ziyacaylan/Arduino-Kulucka-Makinesi/2.jpg

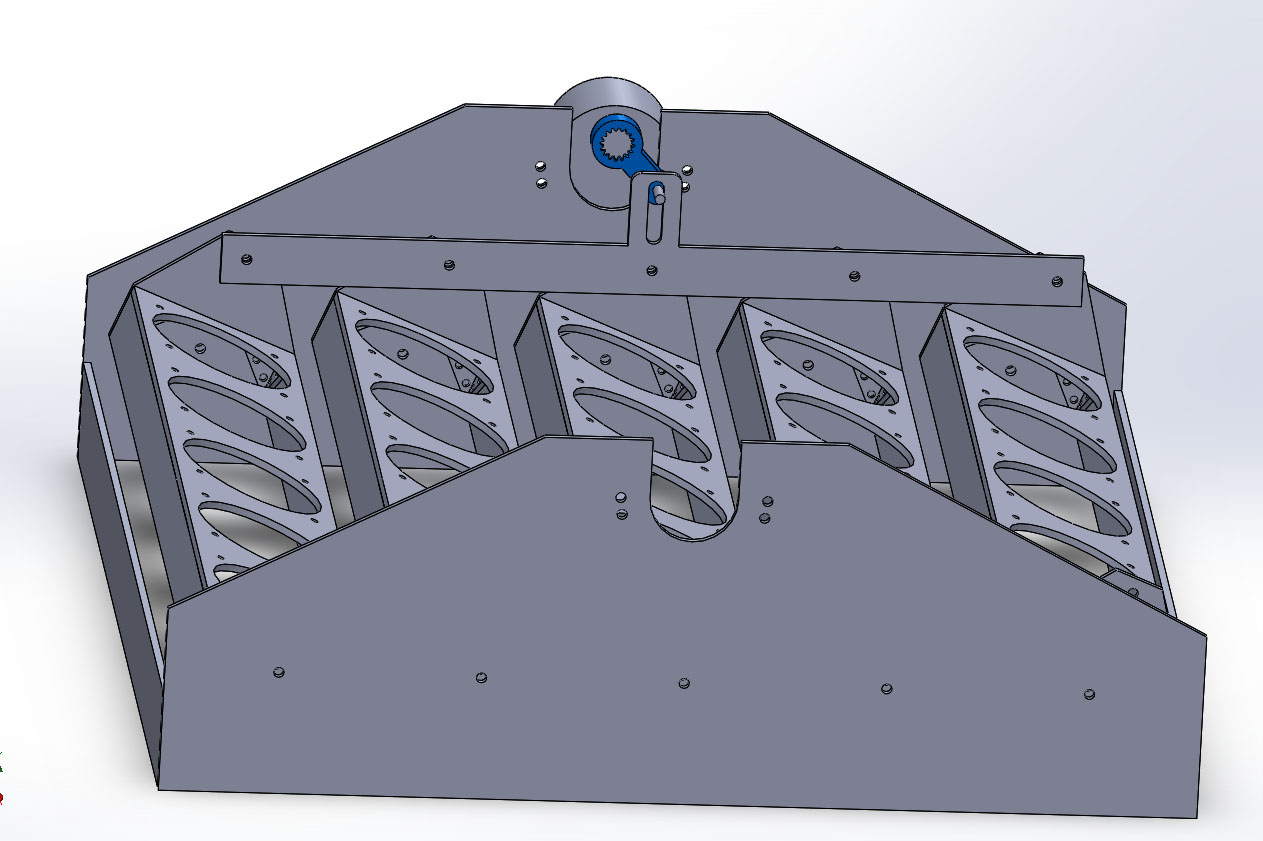
2.jpg
