ziyacaylan/Arduino-Kulucka-Makinesi/20190121_212128.jpg

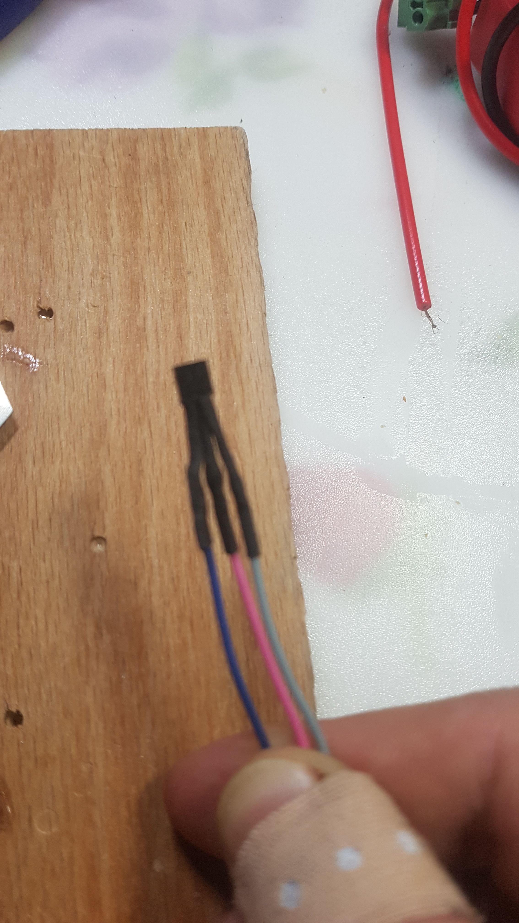
20190121_212128.jpg
