ziyacaylan/Arduino-Kulucka-Makinesi/20190127_220854.jpg

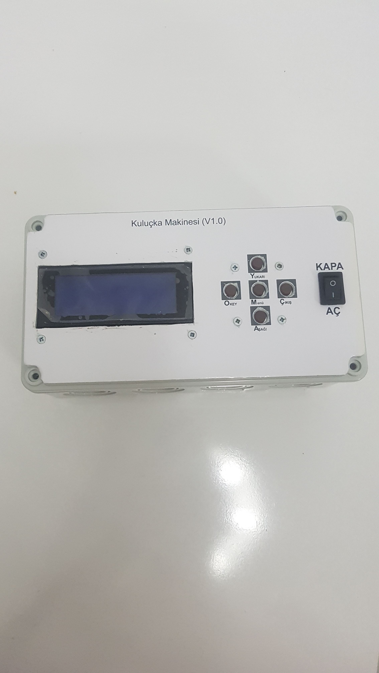
20190127_220854.jpg
