ziyacaylan/Arduino-Kulucka-Makinesi/20190207_001542.jpg

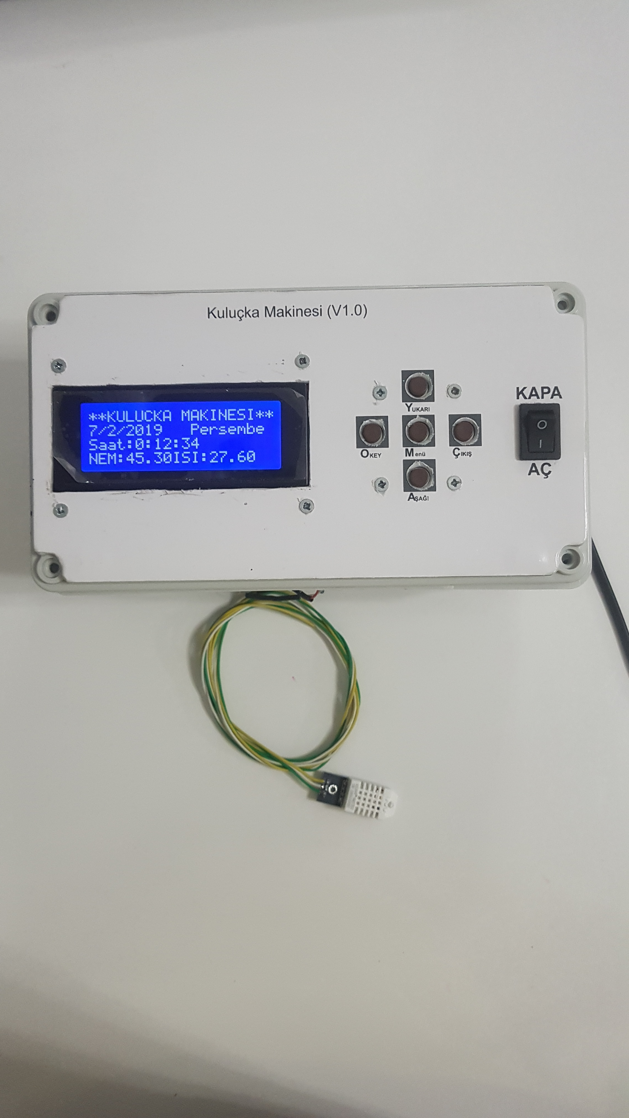
20190207_001542.jpg
