ziyacaylan/Arduino-Kulucka-Makinesi/20190218_220722.jpg

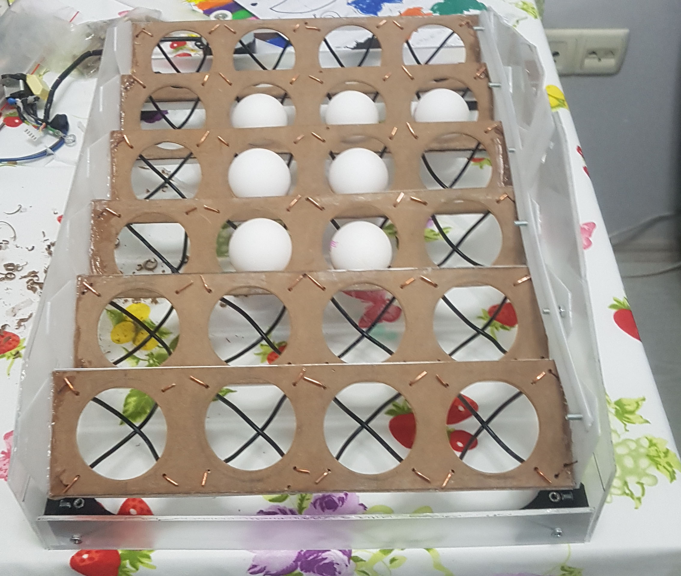
20190218_220722.jpg
