ziyacaylan/Arduino-Kulucka-Makinesi/20190220_000413.jpg

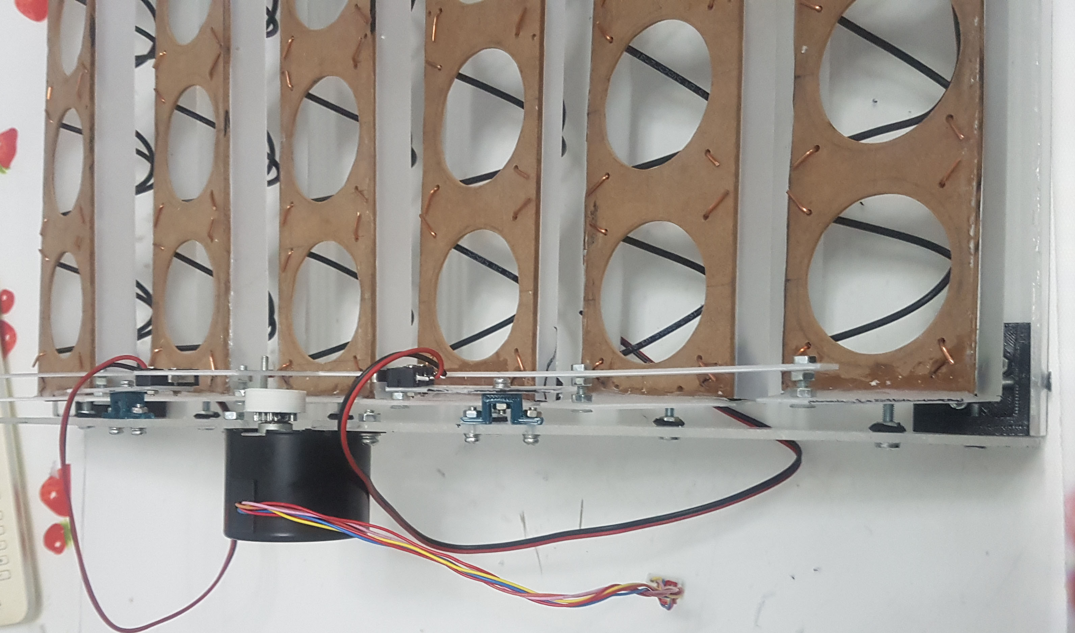
20190220_000413.jpg
