ziyacaylan/Arduino-Kulucka-Makinesi/20190220_000423.jpg

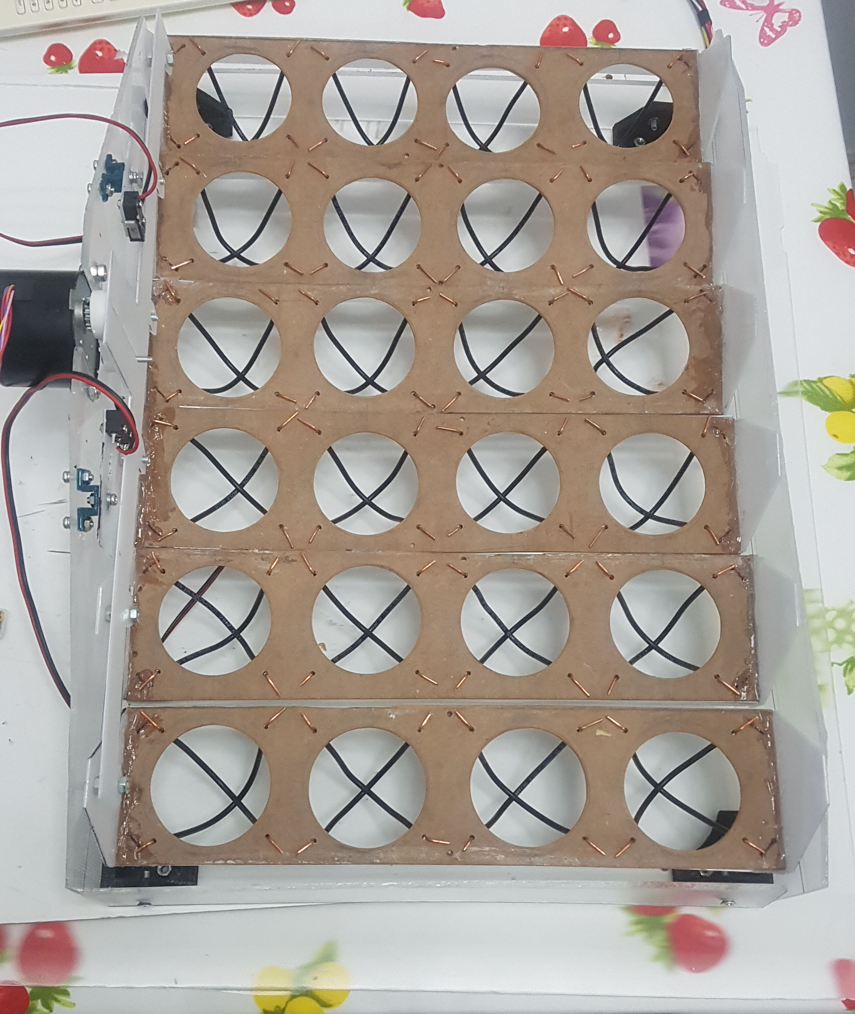
20190220_000423.jpg
