ziyacaylan/Arduino-Kulucka-Makinesi/20190220_000430.jpg

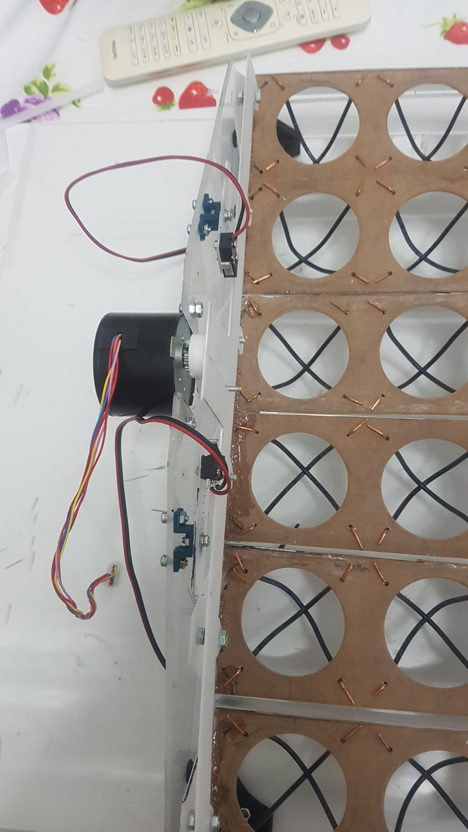
20190220_000430.jpg
