ziyacaylan/Arduino-Kulucka-Makinesi/20190223_140136.jpg

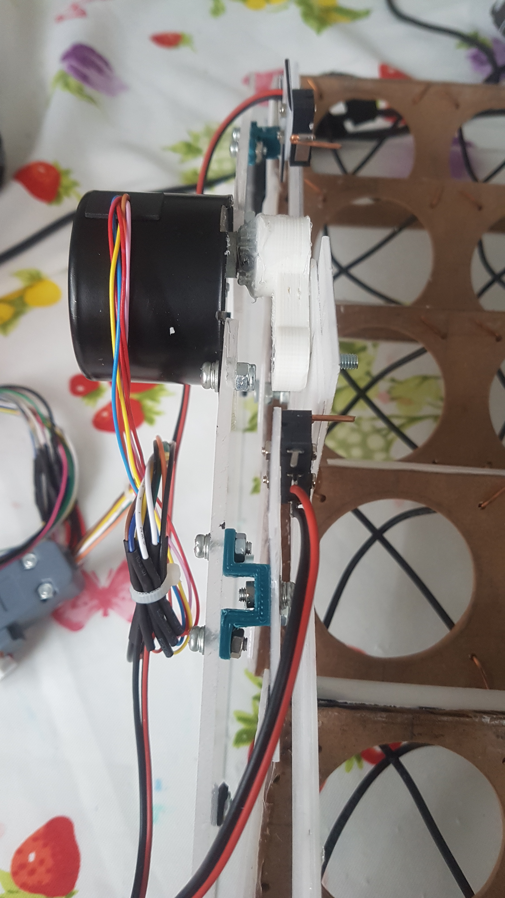
20190223_140136.jpg
