ziyacaylan/Arduino-Kulucka-Makinesi/20190223_140142.jpg

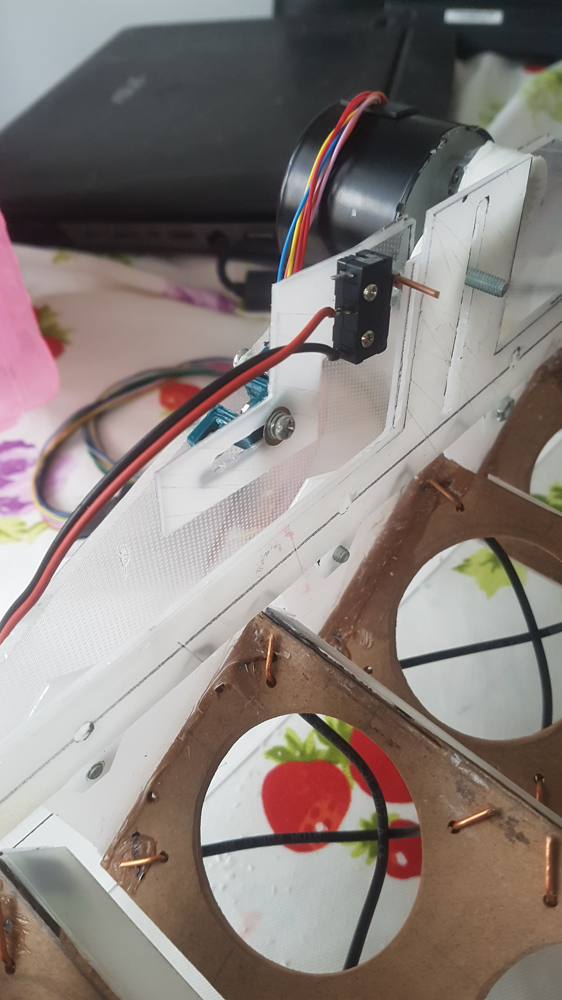
20190223_140142.jpg
