ziyacaylan/Arduino-Kulucka-Makinesi/20190223_140147.jpg

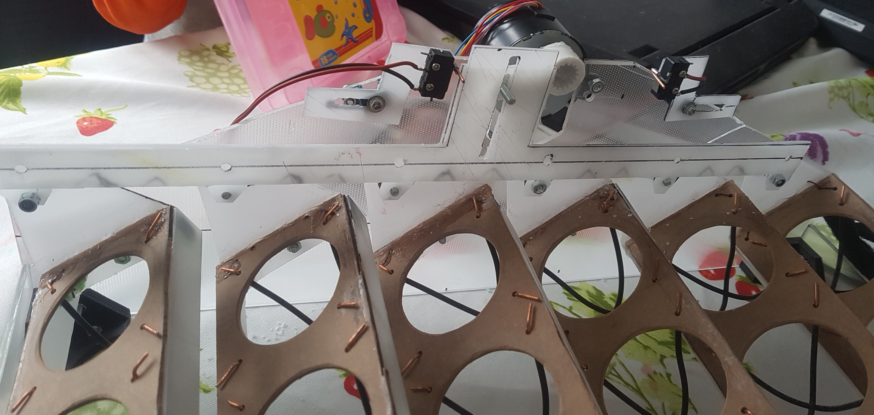
20190223_140147.jpg
