ziyacaylan/Arduino-Kulucka-Makinesi/20190223_140152.jpg

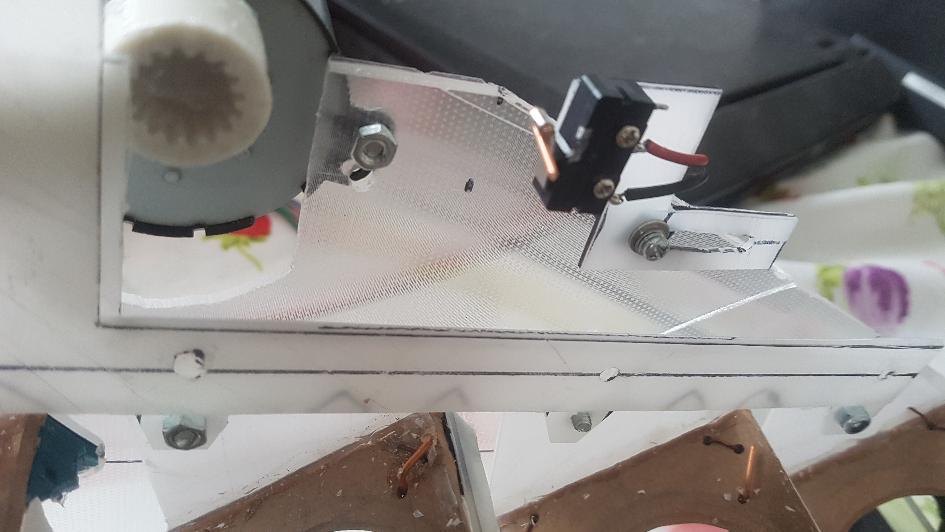
20190223_140152.jpg
