ziyacaylan/Arduino-Kulucka-Makinesi/20190223_140200.jpg

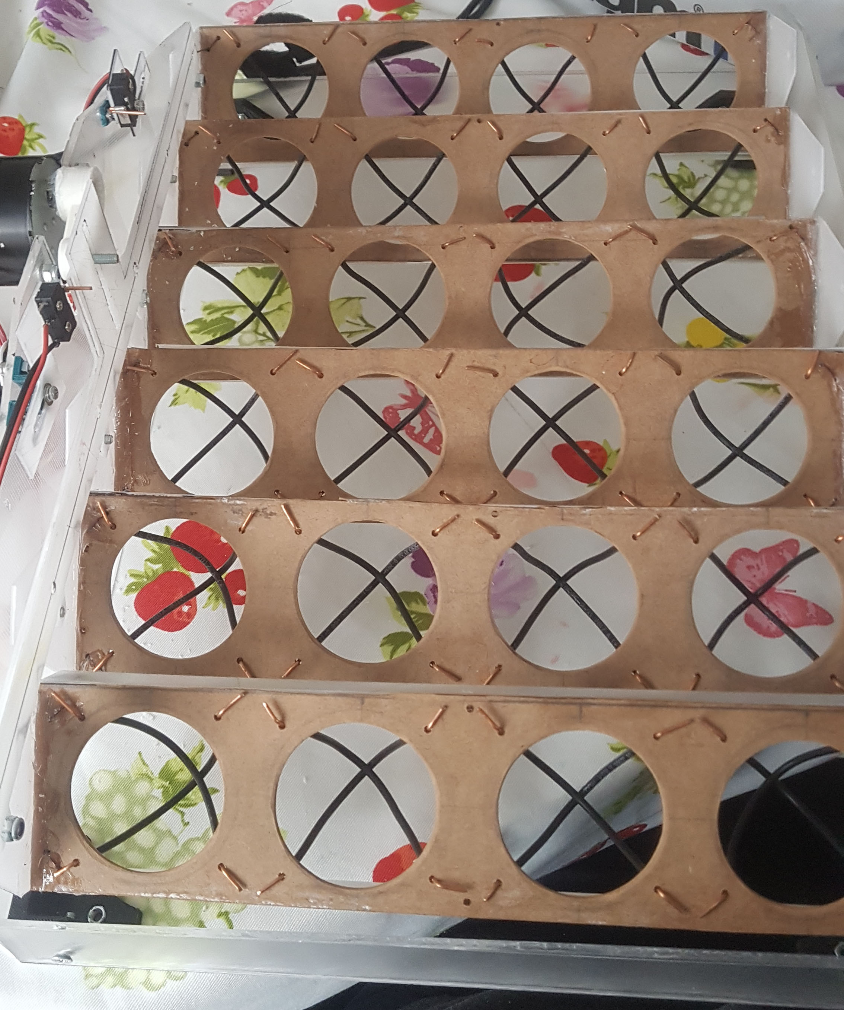
20190223_140200.jpg
