ziyacaylan/Arduino-Kulucka-Makinesi/20190223_235003.jpg

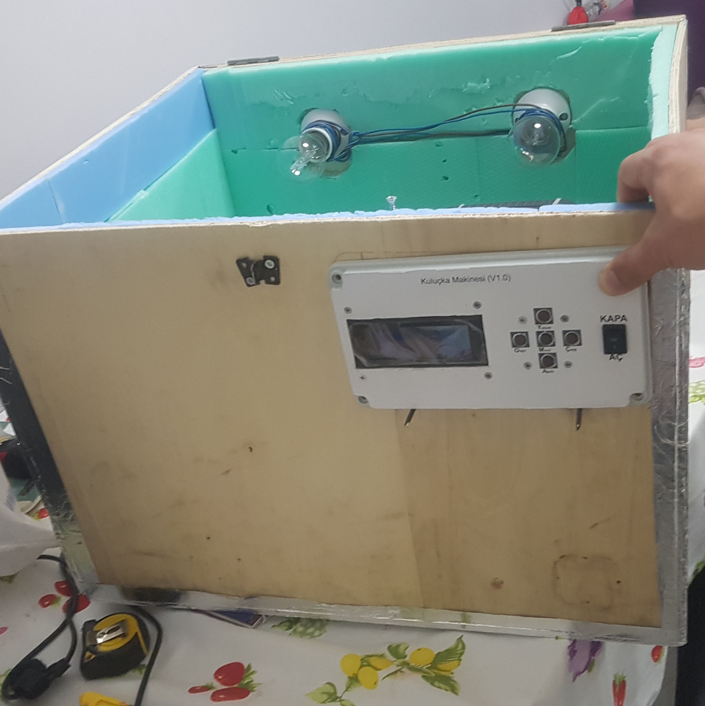
20190223_235003.jpg
