ziyacaylan/Arduino-Kulucka-Makinesi/20190223_235006.jpg

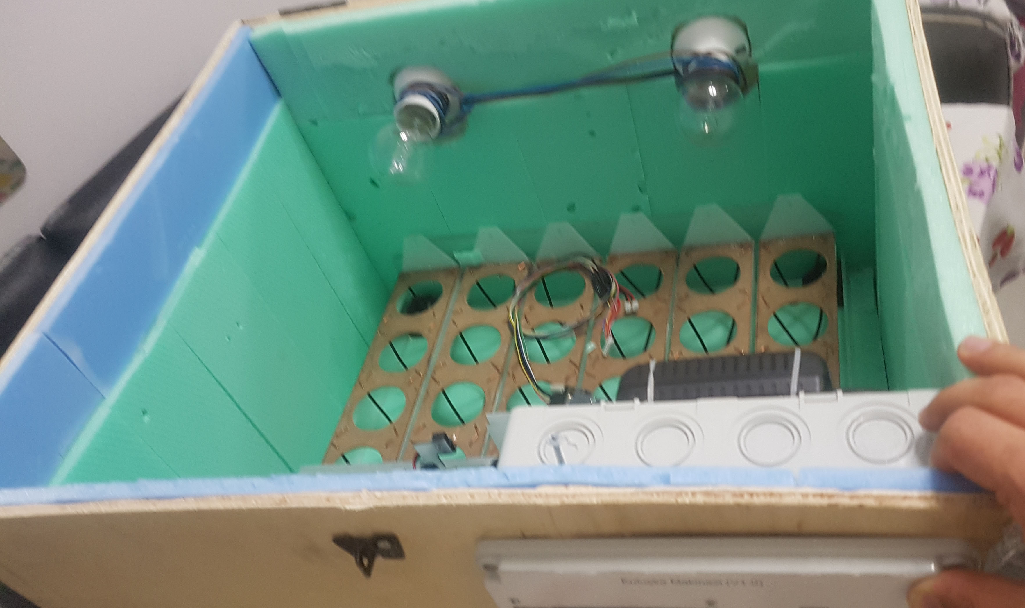
20190223_235006.jpg
