ziyacaylan/Arduino-Kulucka-Makinesi/20190223_235153.jpg

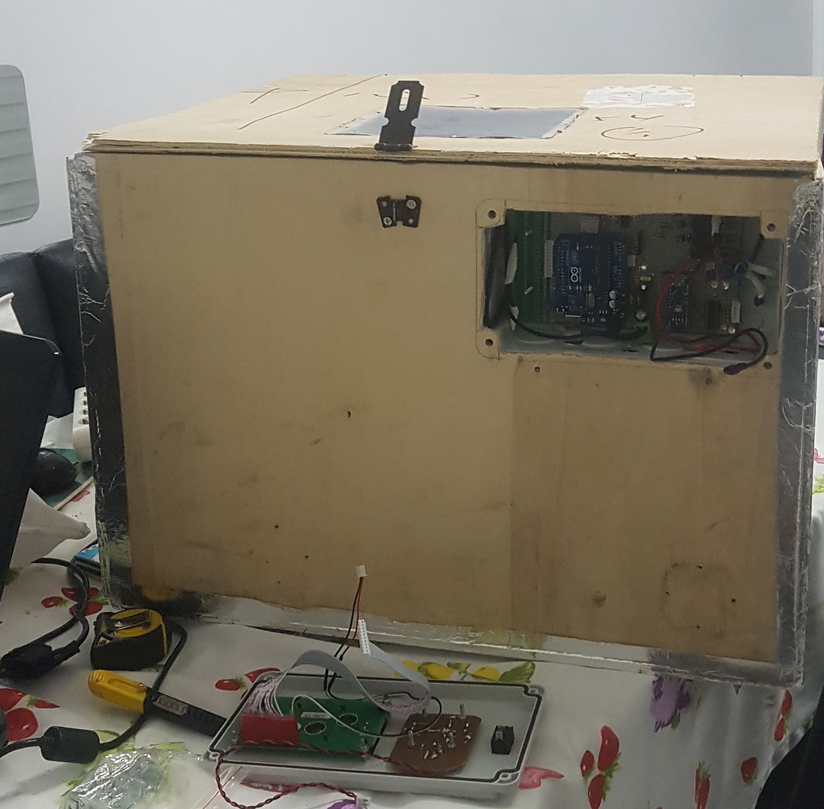
20190223_235153.jpg
