ziyacaylan/Arduino-Kulucka-Makinesi/20190223_235156.jpg

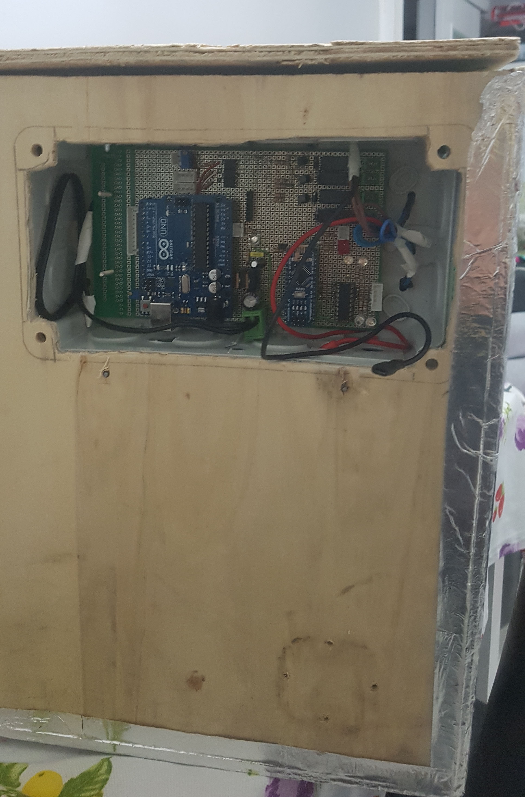
20190223_235156.jpg
