ziyacaylan/Arduino-Kulucka-Makinesi/20190310_233816.jpg

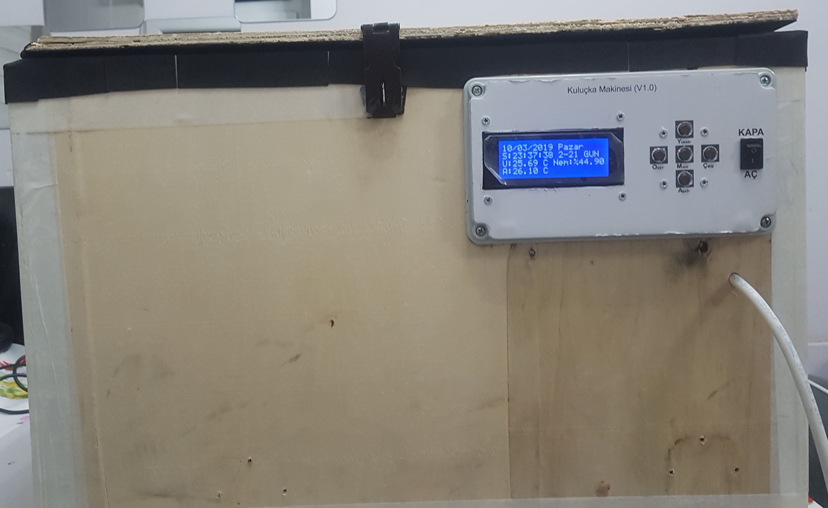
20190310_233816.jpg
