ziyacaylan/Arduino-Kulucka-Makinesi/20190310_233818.jpg

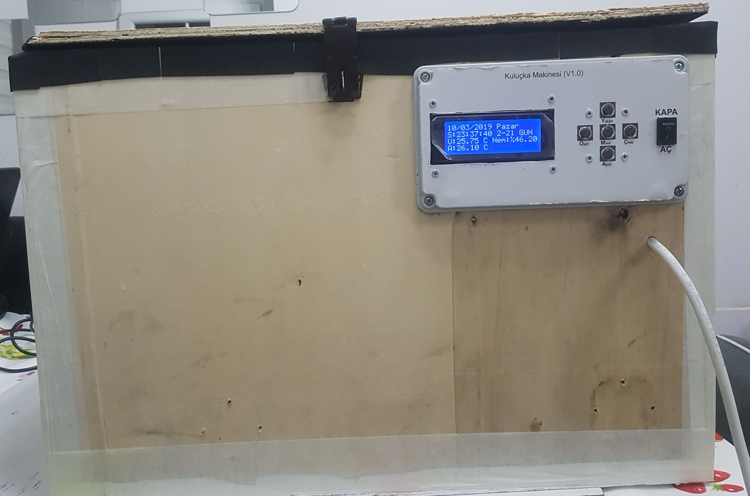
20190310_233818.jpg
