ziyacaylan/Arduino-Kulucka-Makinesi/20190310_233824.jpg

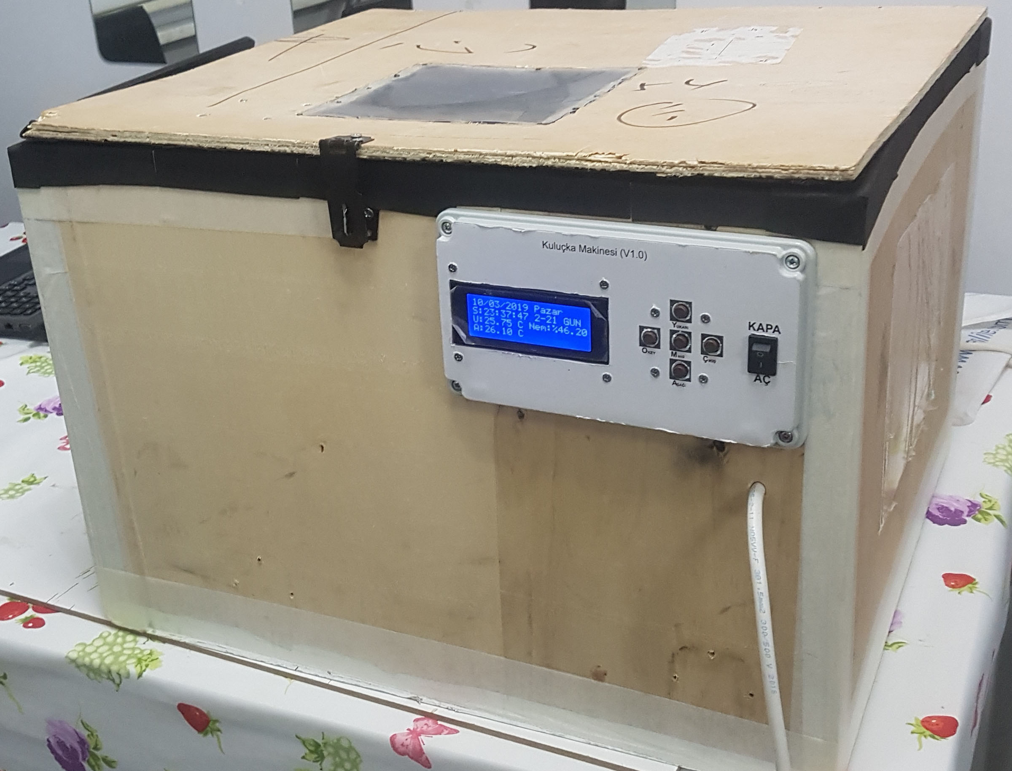
20190310_233824.jpg
