ziyacaylan/Arduino-Kulucka-Makinesi/Başlıksız-1.jpg

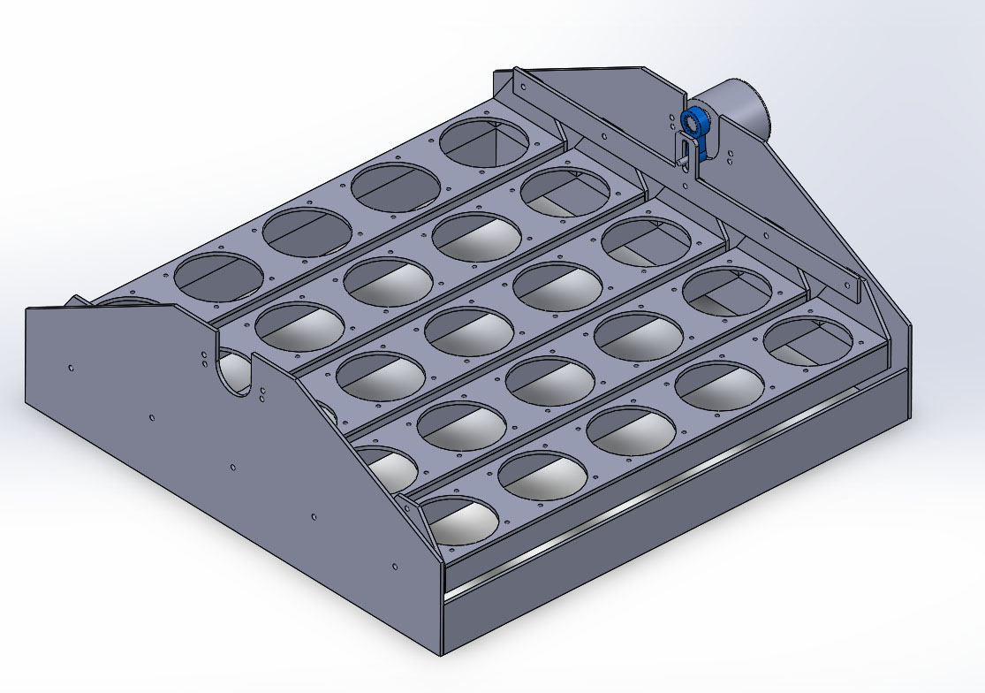
Başlıksız-1.jpg
