ziyacaylan/Arduino-Kulucka-Makinesi/IMG-20190625-WA0006.jpg

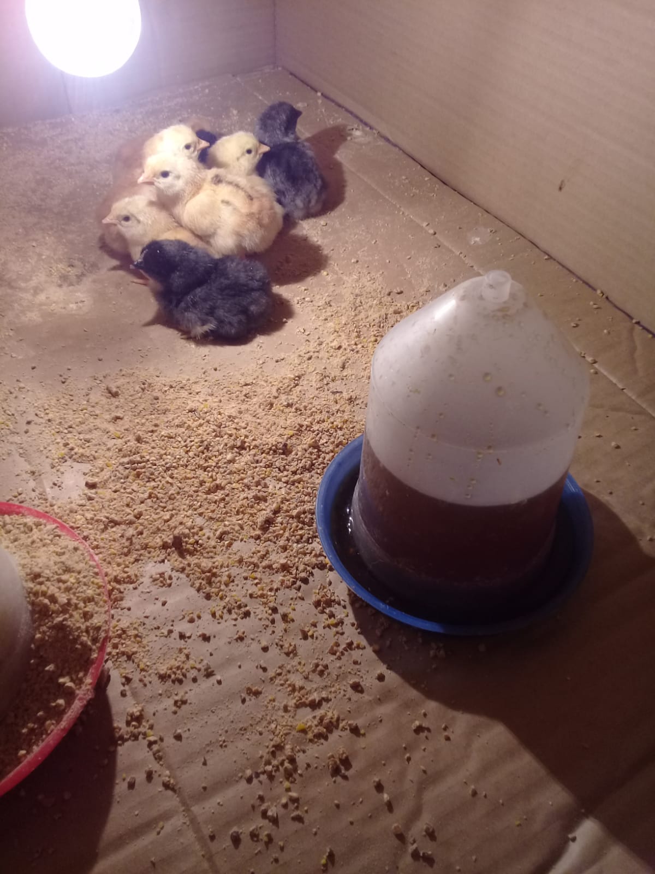
IMG-20190625-WA0006.jpg
