ziyacaylan/Arduino-Kulucka-Makinesi/Viyol_Solid Design/6lı/viyol.SLDPRT

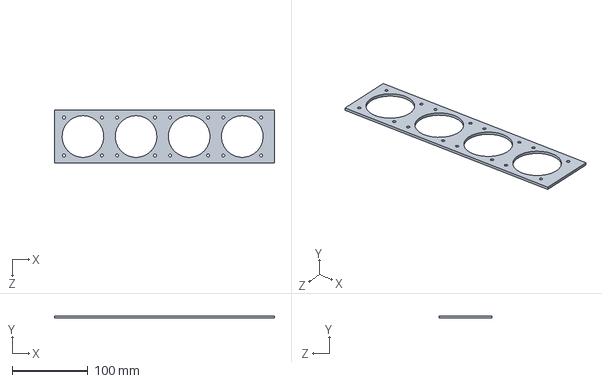
[picture p40: CAD file, 2022-01-30]
Viyol_Solid Design/6lı/viyol.SLDPRT
290.0 x 3.00 x 70.0 mm
