ziyacaylan/Arduino-Kulucka-Makinesi/Viyol_Solid Design/NEW/Viyol_mafsal.SLDPRT

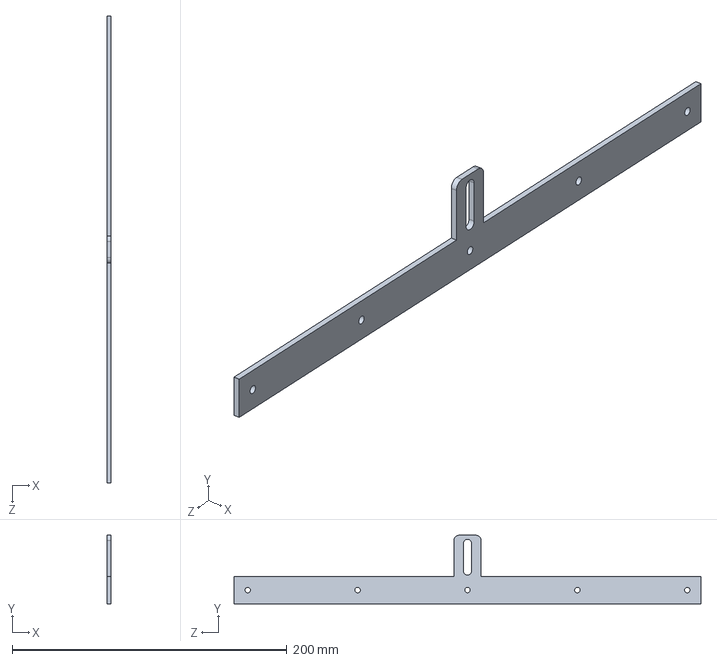
[picture p41: CAD file, 2022-01-30]
Viyol_Solid Design/NEW/Viyol_mafsal.SLDPRT
3.00 x 50.0 x 340.0 mm
