ziyacaylan/Arduino-Kulucka-Makinesi/Viyol_Solid Design/6lı/Sensor_tutucu.SLDPRT

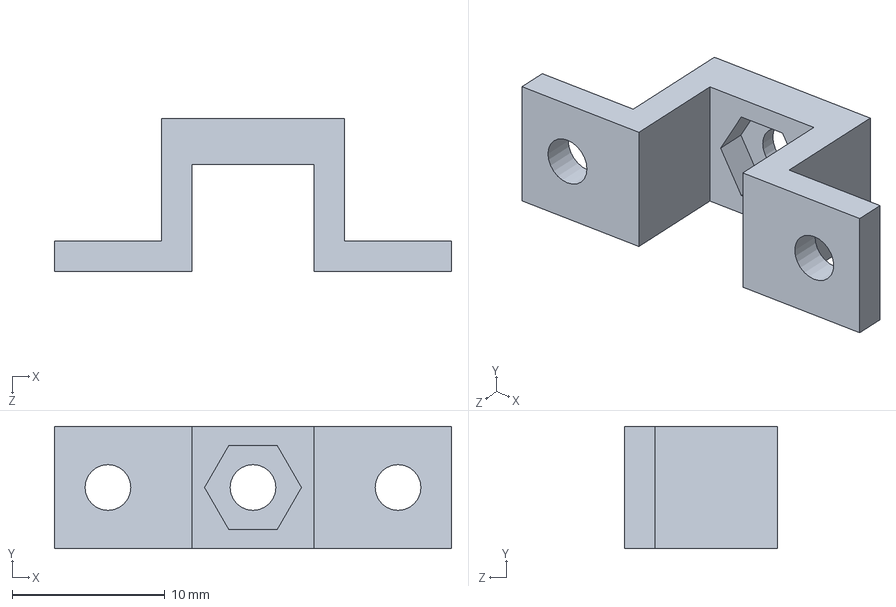
[picture p42: CAD file, 2022-01-30]
Viyol_Solid Design/6lı/Sensor_tutucu.SLDPRT
26.0 x 8.00 x 10.0 mm
