ziyacaylan/Arduino-Kulucka-Makinesi/Viyol_Solid Design/NEW/motor_segman.SLDPRT

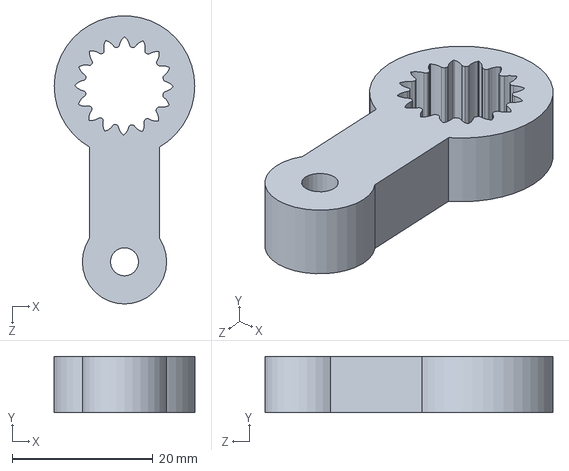
[picture p43: CAD file, 2022-01-30]
Viyol_Solid Design/NEW/motor_segman.SLDPRT
20.0 x 8.00 x 41.0 mm
