ziyacaylan/Arduino-Kulucka-Makinesi/Viyol_Solid Design/6lı/viyol_yanlar.SLDPRT

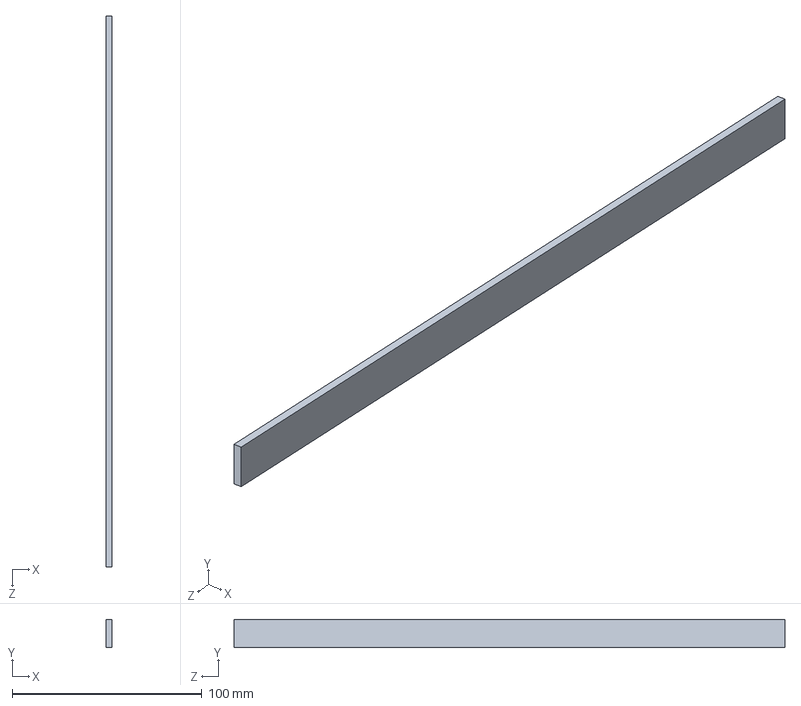
[picture p44: CAD file, 2022-01-30]
Viyol_Solid Design/6lı/viyol_yanlar.SLDPRT
3.00 x 15.0 x 290.0 mm
