ziyacaylan/Arduino-Kulucka-Makinesi/Viyol_Solid Design/NEW/Kasa_yan.SLDPRT

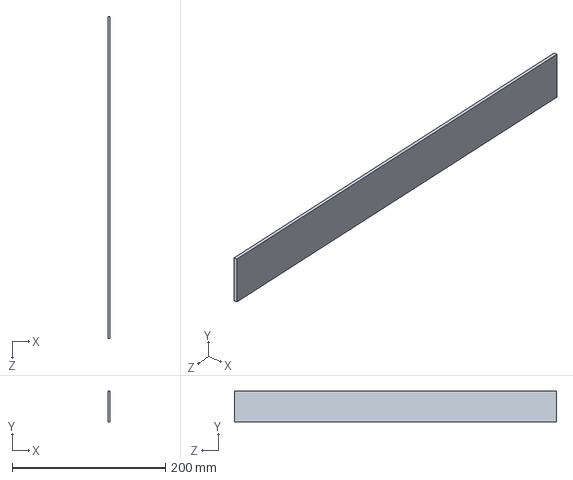
[picture p45: CAD file, 2022-01-30]
Viyol_Solid Design/NEW/Kasa_yan.SLDPRT
3.00 x 40.0 x 420.0 mm
