ziyacaylan/Arduino-Kulucka-Makinesi/Viyol_Solid Design/6lı/Viyol_kasa_arka.SLDPRT

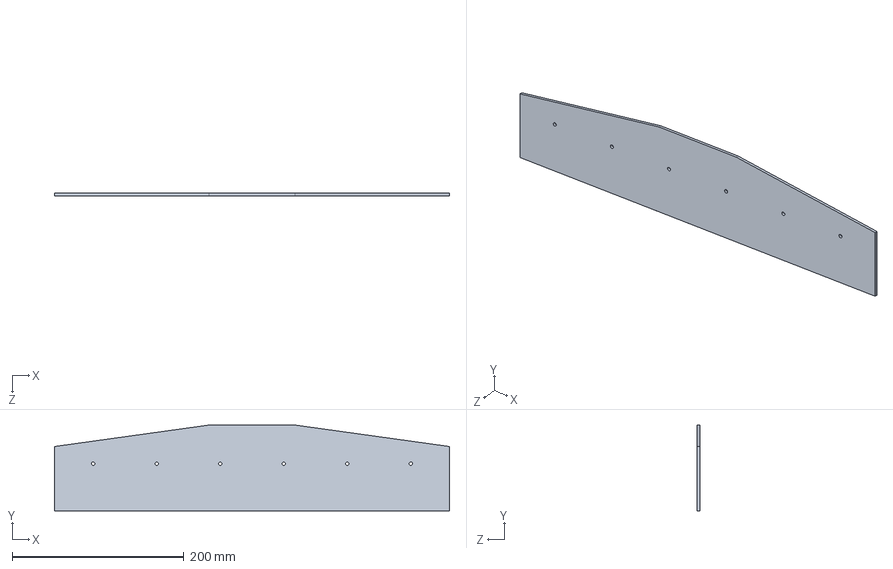
[picture p46: CAD file, 2022-01-30]
Viyol_Solid Design/6lı/Viyol_kasa_arka.SLDPRT
460.0 x 100.0 x 3.00 mm
