ziyacaylan/Arduino-Kulucka-Makinesi/Viyol_Solid Design/6lı/viyol_mafsal.SLDPRT

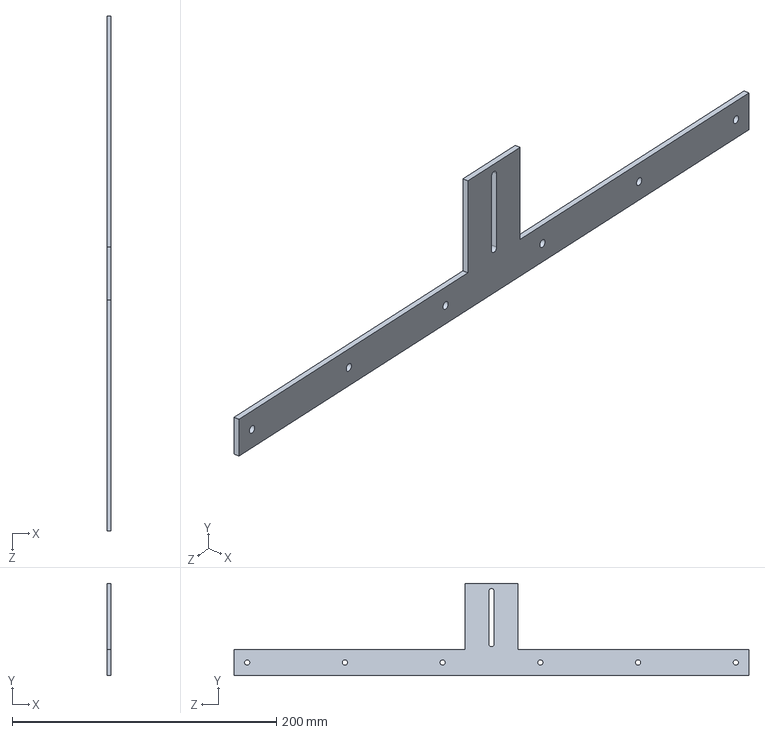
[picture p47: CAD file, 2022-01-30]
Viyol_Solid Design/6lı/viyol_mafsal.SLDPRT
3.00 x 70.0 x 390.0 mm
