ziyacaylan/Arduino-Kulucka-Makinesi/Viyol_Solid Design/NEW/yiyol.SLDPRT

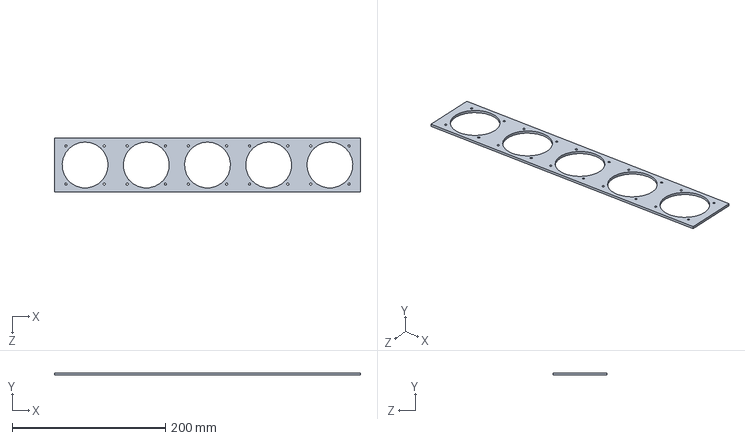
[picture p48: CAD file, 2022-01-30]
Viyol_Solid Design/NEW/yiyol.SLDPRT
400.0 x 3.00 x 70.0 mm
