ziyacaylan/Arduino-Kulucka-Makinesi/Viyol_Solid Design/NEW/viyol_destek.SLDPRT

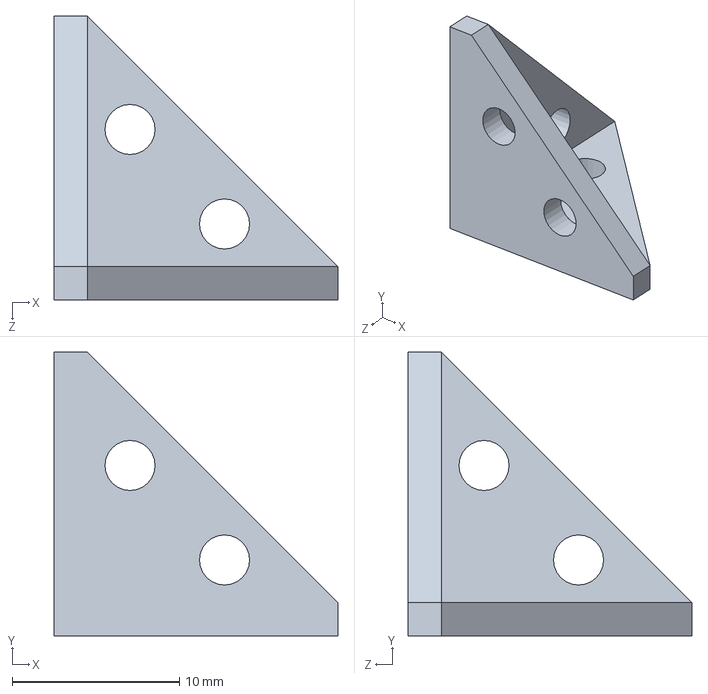
[picture p49: CAD file, 2022-01-30]
Viyol_Solid Design/NEW/viyol_destek.SLDPRT
17.0 x 17.0 x 17.0 mm
