ziyacaylan/Arduino-Kulucka-Makinesi/Viyol_Solid Design/6lı/Kasa_yanlar.SLDPRT

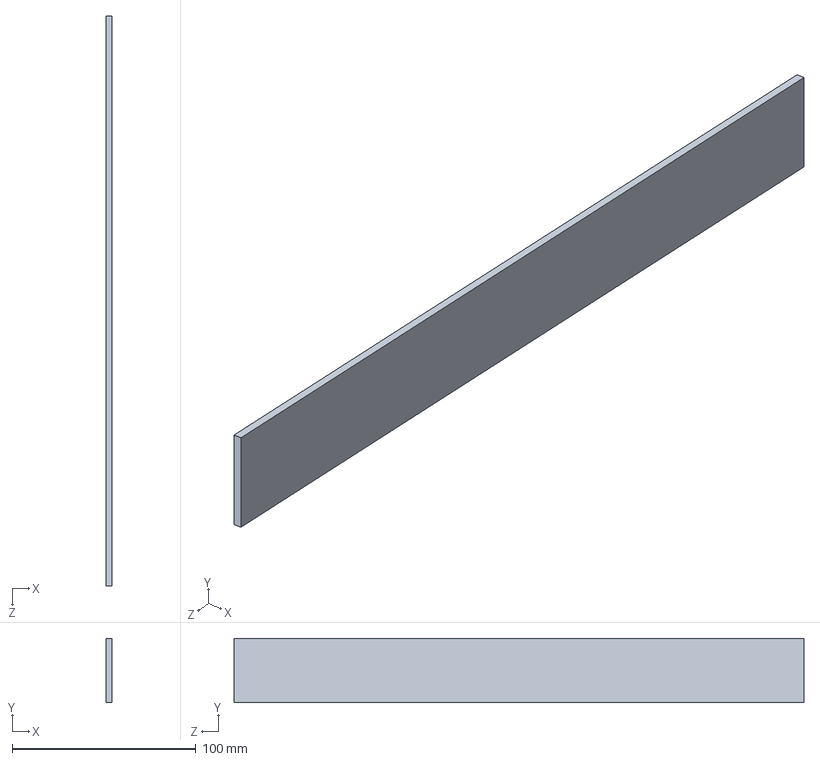
[picture p50: CAD file, 2022-01-30]
Viyol_Solid Design/6lı/Kasa_yanlar.SLDPRT
3.00 x 35.0 x 310.0 mm
